dkuaegis/aegis-hack-the-badge/assets/brand/sponsors/official-kit/easyeda/EasyEDA_Horz_W_Trans.png

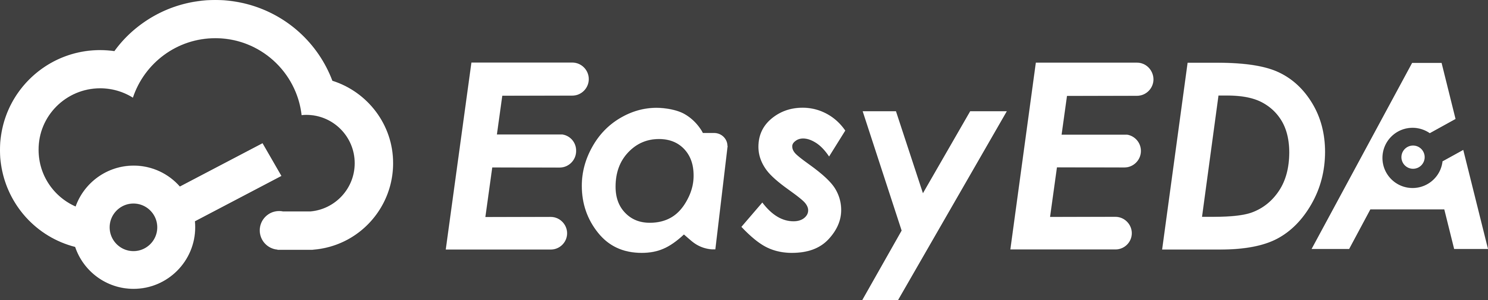
assets/brand/sponsors/official-kit/easyeda/EasyEDA_Horz_W_Trans.png
