dkuaegis/aegis-hack-the-badge/assets/brand/sponsors/official-kit/easyeda/EasyEDA_Vert_Blue_WhiteBG.png

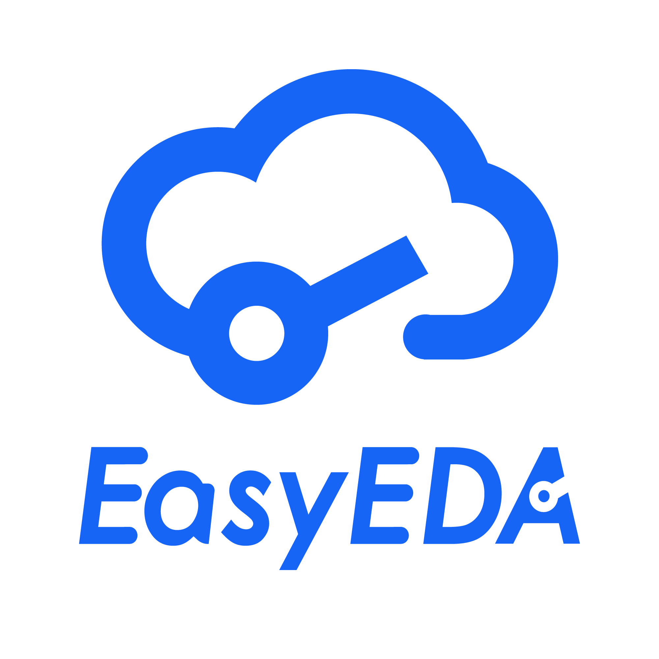
assets/brand/sponsors/official-kit/easyeda/EasyEDA_Vert_Blue_WhiteBG.png
